gggguilherme/kontroller/Source/3D Models/stl/Translation Control/Y Stick.stl

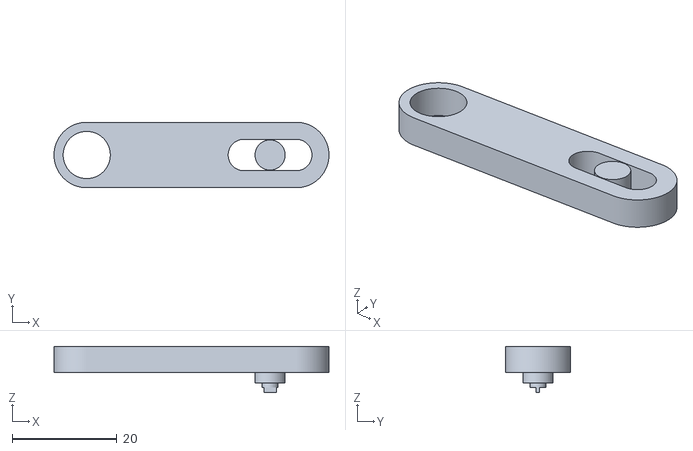
[picture p16: CAD file, 2022-03-01]
Source/3D Models/stl/Translation Control/Y Stick.stl
52.5 x 12.5 x 8.80
