gggguilherme/kontroller/Source/3D Models/STEP/Imports/Display _ DC(DA)56-11.stp

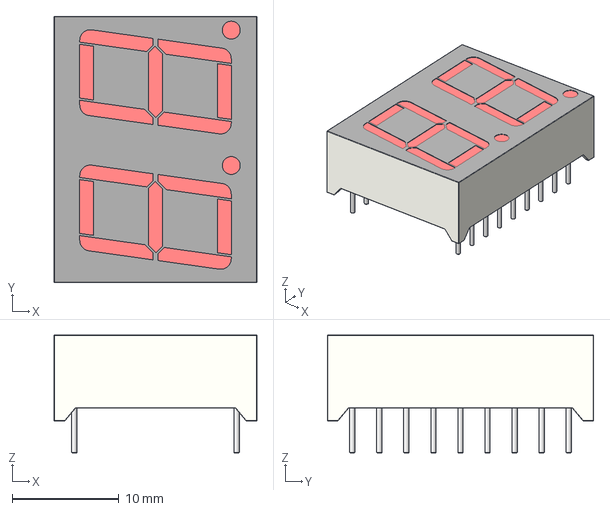
[picture p17: CAD file, 2022-03-01]
Source/3D Models/STEP/Imports/Display _ DC(DA)56-11.stp
19.1 x 25.0 x 11.1 mm
