gggguilherme/kontroller/Source/3D Models/stl/Throttle Lever/Interface3.stl

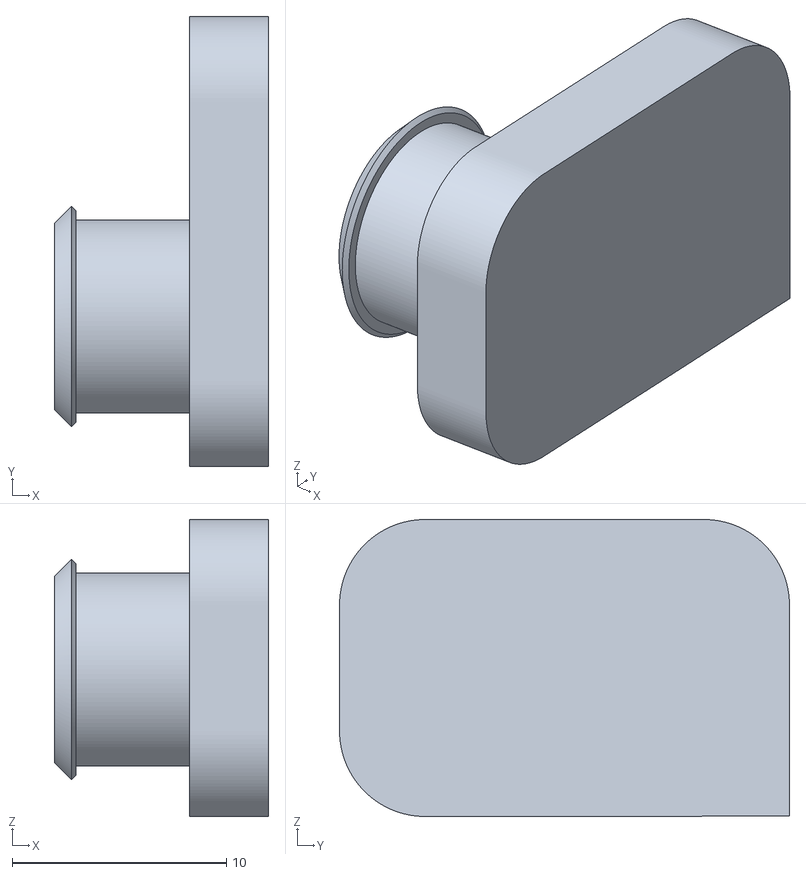
[picture p18: CAD file, 2022-03-07]
Source/3D Models/stl/Throttle Lever/Interface3.stl
10.00 x 21.0 x 13.9
