gggguilherme/kontroller/Source/3D Models/stl/Translation Control/Z Stick.stl

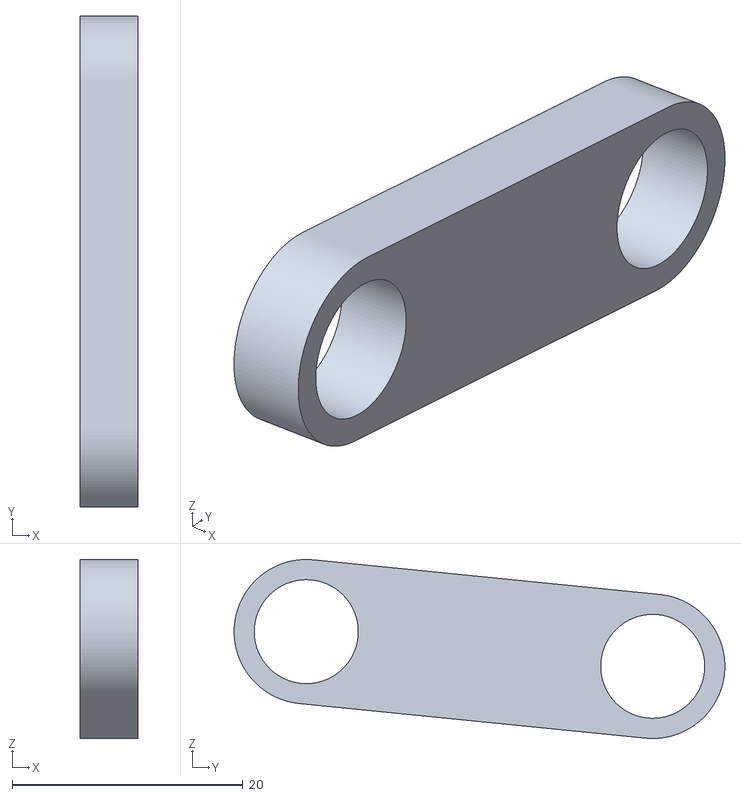
[picture p19: CAD file, 2022-03-01]
Source/3D Models/stl/Translation Control/Z Stick.stl
5.00 x 42.5 x 15.5
