gggguilherme/kontroller/Source/3D Models/STEP/Imports/SPDT-Print-Switch.step

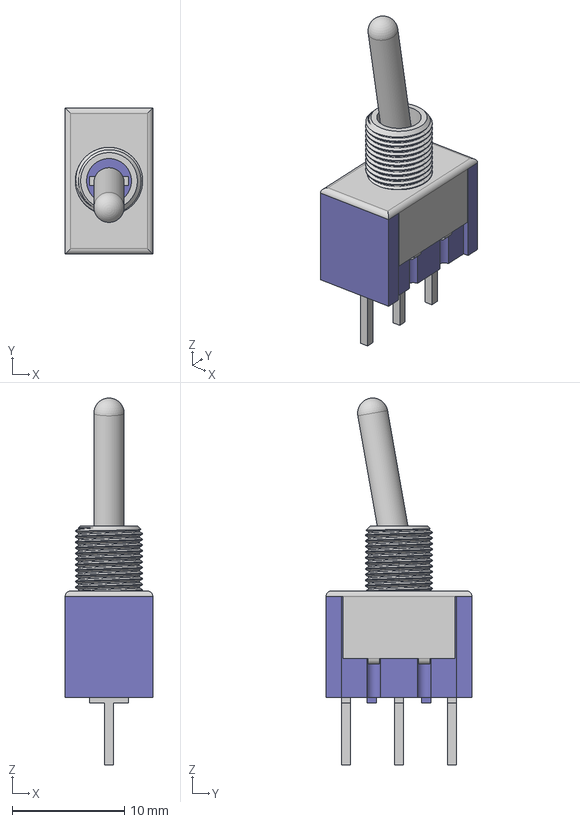
[picture p20: CAD file, 2022-03-01]
Source/3D Models/STEP/Imports/SPDT-Print-Switch.step
7.80 x 13.0 x 32.7 mm
Plastic_Housing
Pin2
Pin1
Pin3
Shield
Shaft
