gggguilherme/kontroller/Source/3D Models/stl/Translation Control/Pivot2.stl

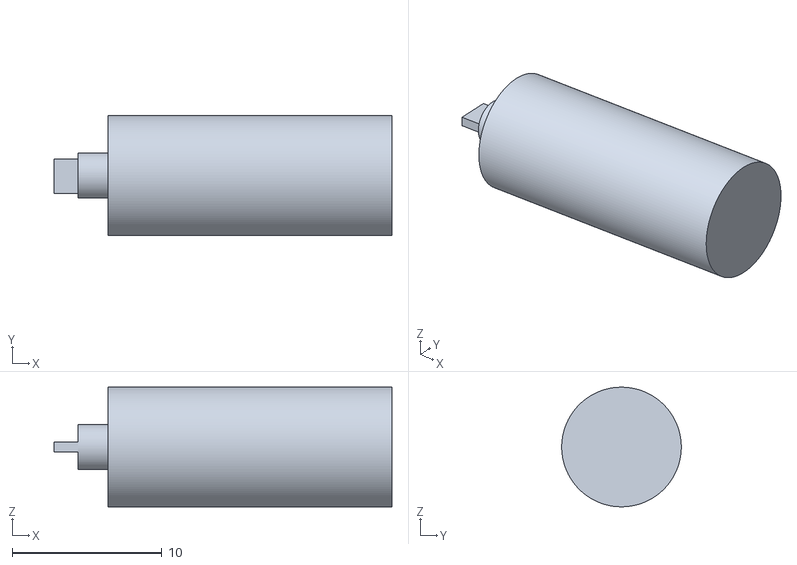
[picture p21: CAD file, 2022-03-01]
Source/3D Models/stl/Translation Control/Pivot2.stl
22.6 x 8.00 x 8.00
