gggguilherme/kontroller/Source/3D Models/stl/Translation Control/Support.stl

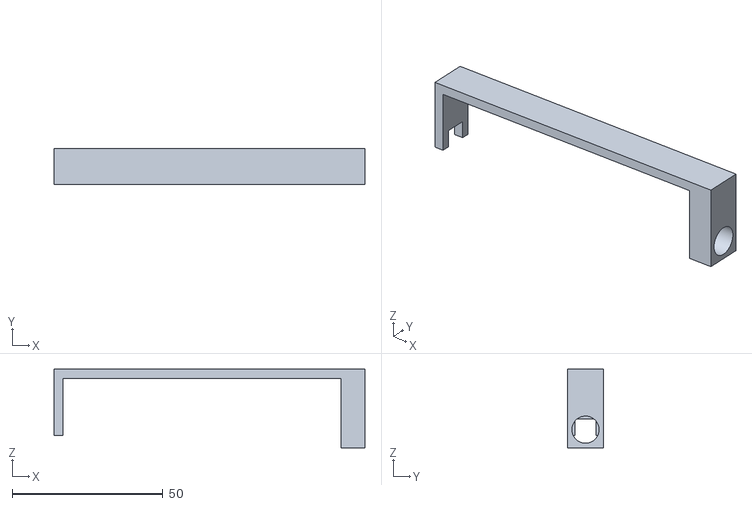
[picture p22: CAD file, 2022-03-01]
Source/3D Models/stl/Translation Control/Support.stl
103.0 x 12.0 x 26.0
