gggguilherme/kontroller/Source/3D Models/stl/Translation Control/X Stick.stl

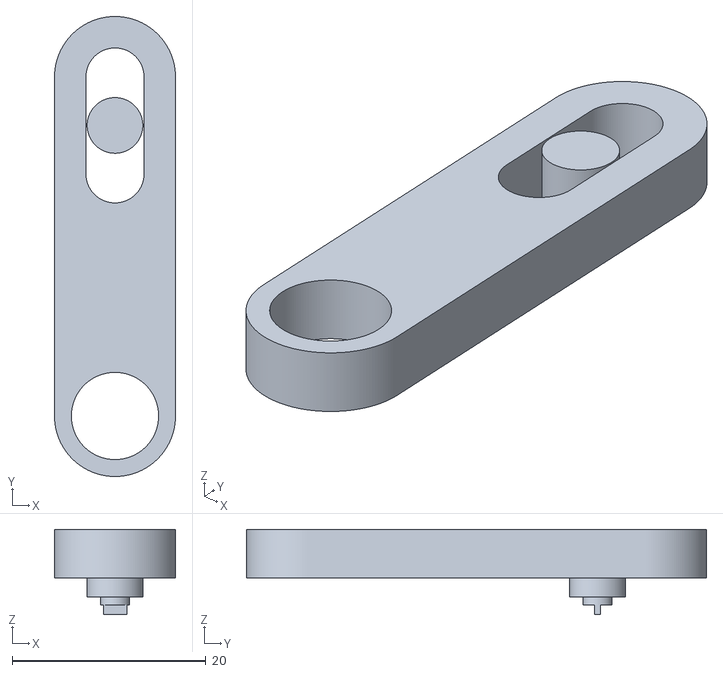
[picture p23: CAD file, 2022-03-01]
Source/3D Models/stl/Translation Control/X Stick.stl
12.5 x 47.5 x 8.80
