gggguilherme/kontroller/Source/3D Models/stl/Translation Control/Pivot1.stl

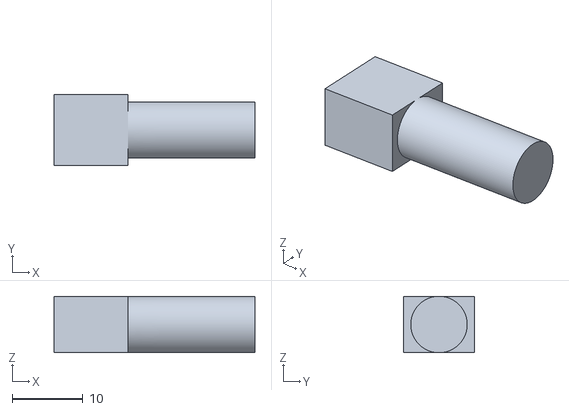
[picture p24: CAD file, 2022-03-01]
Source/3D Models/stl/Translation Control/Pivot1.stl
28.5 x 10.0 x 8.00
